xreef/BatteryCapacityTesterArduinoNANO/Resources/batteryInfo/rv-battery-open-circuit-voltage.png

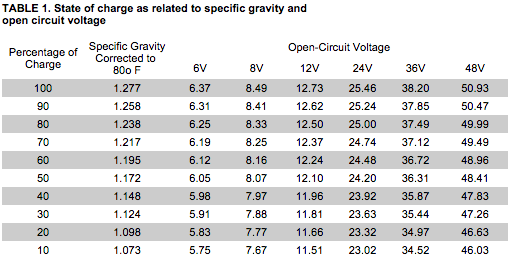
Resources/batteryInfo/rv-battery-open-circuit-voltage.png
