xreef/BatteryCapacityTesterArduinoNANO/Resources/v02/PB_01_pin_bottom.jpg

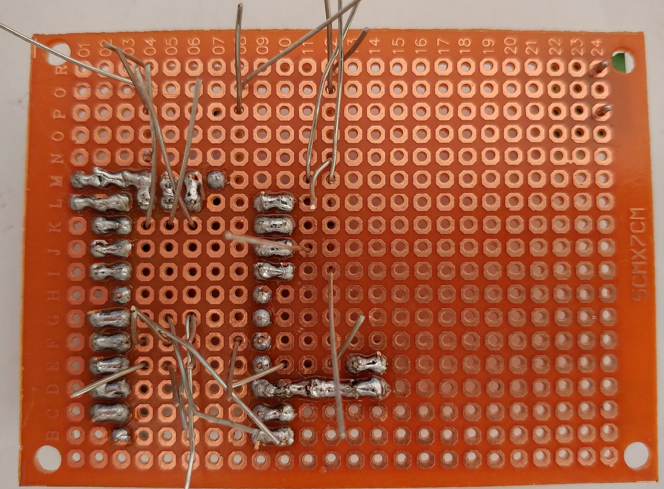
Resources/v02/PB_01_pin_bottom.jpg
