xreef/BatteryCapacityTesterArduinoNANO/Resources/v02/PB_03_pulldown_up.jpg

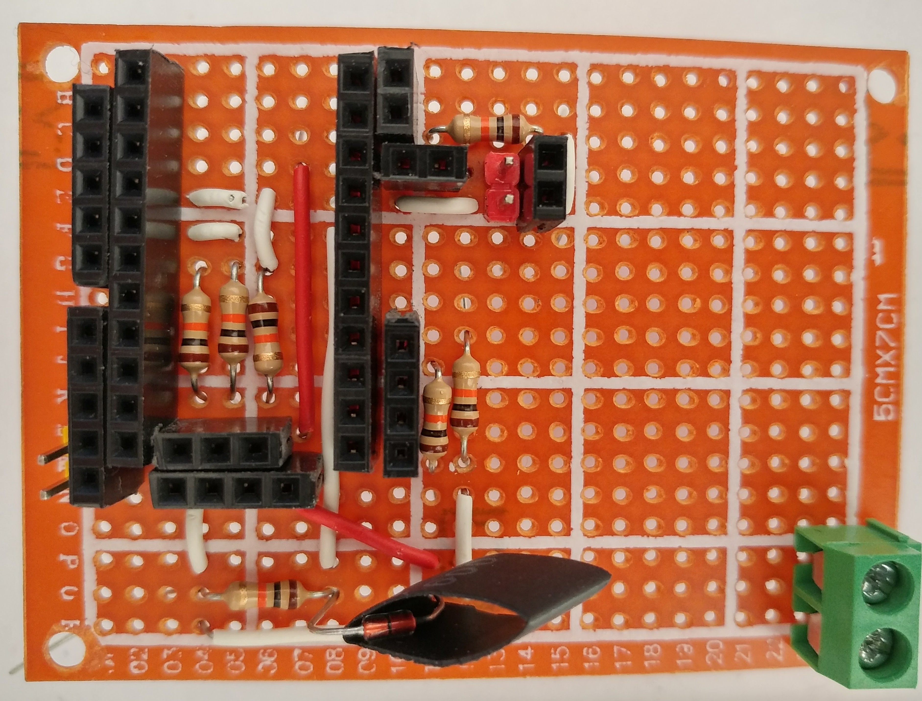
Resources/v02/PB_03_pulldown_up.jpg
