xreef/BatteryCapacityTesterArduinoNANO/BatteryCapacityTesterArduinoNANO.h

// Only modify this file to include
// - function definitions (prototypes)
// - include files
// - extern variable definitions
// In the appropriate section

#ifndef _BatteryTesterArduinoUNO_H_
#define _BatteryTesterArduinoUNO_H_
#include "Arduino.h"
//add your includes for the project BatteryTesterArduinoUNO here


//end of add your includes here


//add your function definitions for the project BatteryTesterArduinoUNO here




//Do not add code below this line
#endif /* _BatteryTesterArduinoUNO_H_ */
